FLRHW/StepUp_module_12to450V/Supporting docs/11.66 kOhm load/15.01.2026 07.36.41.png

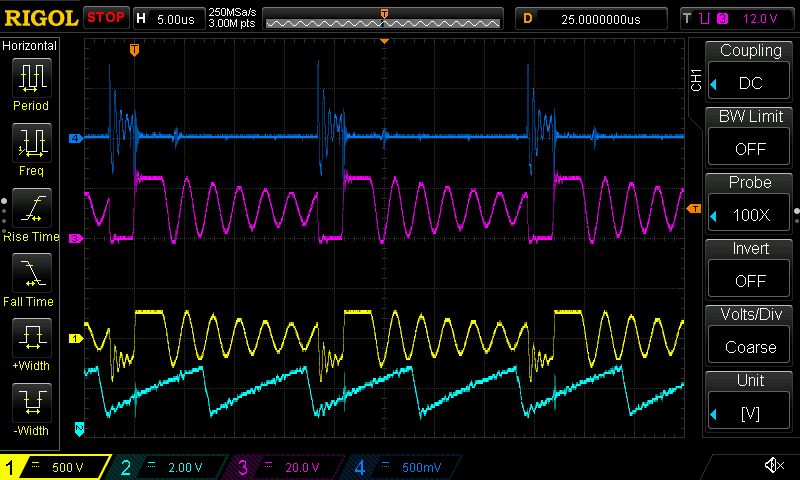
Supporting docs/11.66 kOhm load/15.01.2026 07.36.41.png
