FLRHW/StepUp_module_12to450V/Supporting docs/870 Ohm load/15.01.2026 07.36.52.png

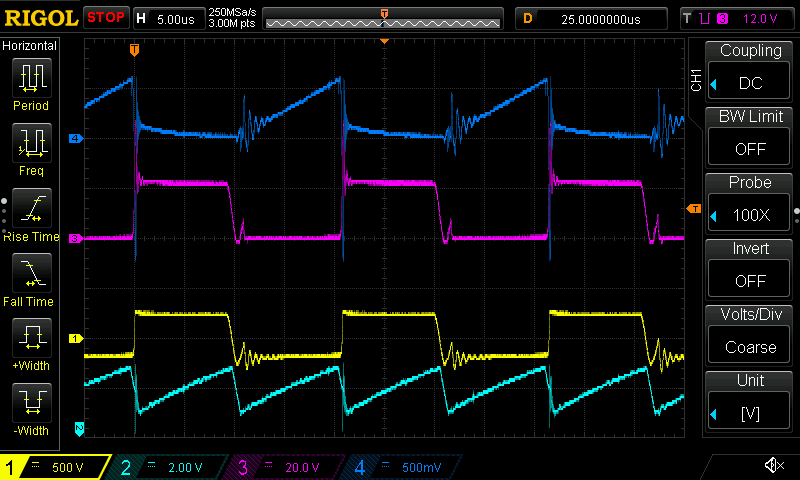
Supporting docs/870 Ohm load/15.01.2026 07.36.52.png
