FLRHW/StepUp_module_12to450V/HTML/images/cat_png_3d_viewer_bottom_StepUp_module_12to450V-bottom.png

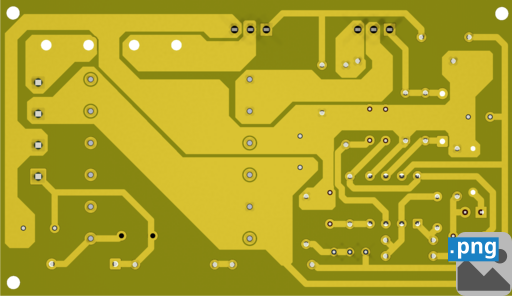
HTML/images/cat_png_3d_viewer_bottom_StepUp_module_12to450V-bottom.png
