FLRHW/StepUp_module_12to450V/HTML/images/cat_png_3d_viewer_top_StepUp_module_12to450V-top.png

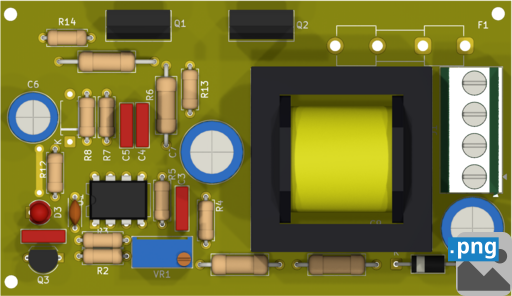
HTML/images/cat_png_3d_viewer_top_StepUp_module_12to450V-top.png
